zanegolas/Interface_Design/src/ZGObjectTracker.h

//
// ZGObjectTracker.h
// Teensy 4.1
//
// Created by Zane Golas on 4/7/23.
// Copyright (c) 2023 Zane Golas. All rights reserved.
//

#include <Arduino.h>
#include <rplidar_driver_impl.h>
#include <vector>
#include <cmath>
#include "ZGObject.h"
#include <unordered_map>

#pragma once

/**
 * @brief Used for processing point cloud buffers to create clusters which are then matched to internally tracked objects or
 * used to create a new object if no match is found. This class also updates and sends Midi data derived from positional
 * information of the tracked object.
 */

class ZGObjectTracker {
public:
    /* */
    ZGObjectTracker();

    /* */
    ~ZGObjectTracker();

    /**
     * @brief Called once per 360 degree scan to find objects in the point cloud buffer and send midi data
     * @param inBuffer Polar point data from the lidar. This function will clear the buffer when processing is finished
     * */
    void processBuffer(std::vector<ZGPolarData>& inBuffer);

    /**
     * @return A const reference to the clusters found by the object tracker. Intended for plotting on LCD.
     */
    const std::vector<std::vector<ZGPoint>> &getClusters() const;

    /**
     * @return A const reference to the objects currently tracked. Intended for plotting on LCD.
     */
    const std::vector<ZGObject> &getObjects() const;

    const float& getMaxDistance() const;

    void setMaxDistance(float inCentimeters);

    const bool& getScanMode() const;

    void setScanMode(bool useDBSCAN);

    const int& getRootNote() const;

    void setRootNote(int inNote);

    const int& getScaleType() const;

    void setScaleType(int inScaleType);

private:

    /**
     * @brief Segments buffer of polar data into clusters using euclidean distance
     * @param inBuffer Buffer will be cleared at the end of the function
     * @see processBuffer()
     */
    void _segmentPointCloud(std::vector<ZGPolarData>& inBuffer);

    /**
     * @brief Utility function to find the center point given a cluster of points
     * @param inCluster A vector of points comprising a cluster
     * @return ZGPoint representing the center of the cluster
     */
    static ZGPoint _findClusterAverage(const std::vector<ZGPoint>& inCluster);

    /**
     * @brief Called after point cloud has been segmented in order to update tracked objects and send midi data
     * @see _segmentPointCloud()
     * @see processBuffer()
     */
    void _updateTrackedObjects();

    float mMaxDistance = 150.f; //in cm
    const float mMaxClusterDistance = 70.f;
    const int mMinPointsPerCluster = 10;
    const float mEpsilon = 30.f;
    int mScaleType = 0;
    int mRootNote = 0;

    bool USE_DBSCAN_METHOD = true;


    std::vector<std::vector<ZGPoint>> mClusters {};
    std::vector<ZGPoint> mPointBuffer {};
    std::vector<ZGObject> mTrackedObjects {};

    void _euclideanScan();

    // DBSCAN Functions //
    int _dbScan();

    std::vector<int> _calculateCluster(ZGPoint point);

    int _expandCluster(ZGPoint &inPoint, int clusterID);


};
