zanegolas/Interface_Design/src/ZGObject.h

//
// ZGObject.h
// Teensy 4.1
//
// Created by Zane Golas on 4/12/23.
// Copyright (c) 2023 Zane Golas. All rights reserved.
//

#pragma once
#include <Arduino.h>
#include "ZGConversionHelpers.h"


class ZGObject {
public:

    ZGObject(float inX, float inY, int inRoot, int inScaleType, float inDistance);

    ~ZGObject();

    void updatePoint(ZGPoint inPoint);

    const float& getX() const;

    const float& getY() const;

    ZGPoint getPoint() const;

    void flagForRemoval(bool inShouldRemove);

    const bool& requestToRemove() const;

    void updateRootNote(int inNewRoot);

    void updateDistance(float inNewDistance);

    void updateScaleType(int inNewType);

private:

    float mX = 0;
    float mY = 0;
    float mSpeed = 0;
    float mAngle = 0;
    float mAngleSpeed = 0;
    float mDistance = 0;
    float mDistanceSpeed = 0;
    bool mRemoveFlag = false;

    elapsedMillis mSpeedTracker = 0;

    double midi_factor = 12. / 360.;
    float mod_factor = 127.f / 150.f;

    //MIDI
    int currentMidiNote = 0;
    int newMidiNote = 0;
    int mMidiChannel = 1;
    int modValue = 0;
    int timbreValue = 63;

    int mRootNote = 48; //C3
    int mScaleType = 0; //Chromatic

    bool _assignMidiChannel();
    void _releaseMidiChannel() const;

    void _calculateMidi();

    void _playMidi();

};
